niconistal/BabyBox/renders/v2-front.png

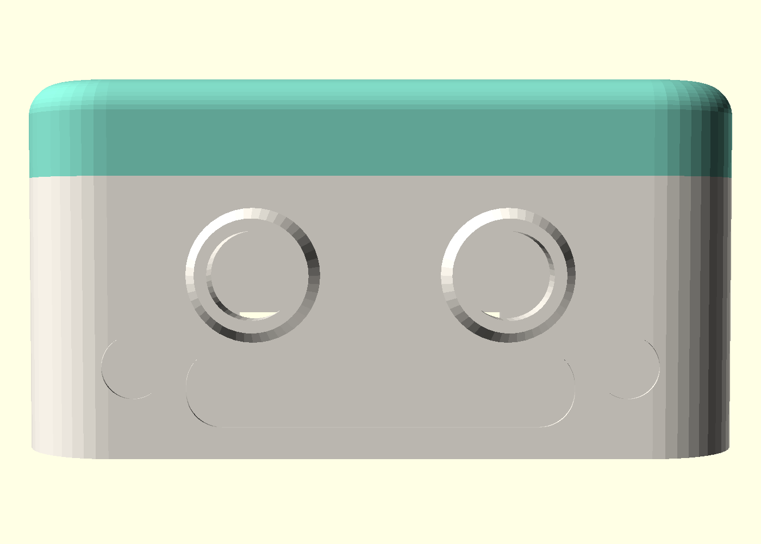
renders/v2-front.png
