niconistal/BabyBox/renders/v2-lid-under.png

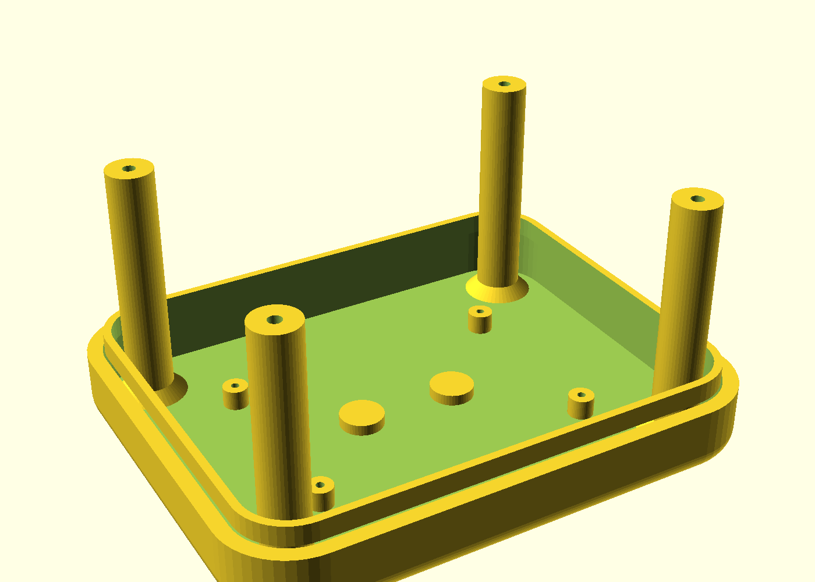
renders/v2-lid-under.png
