niconistal/BabyBox/renders/v3-hero.png

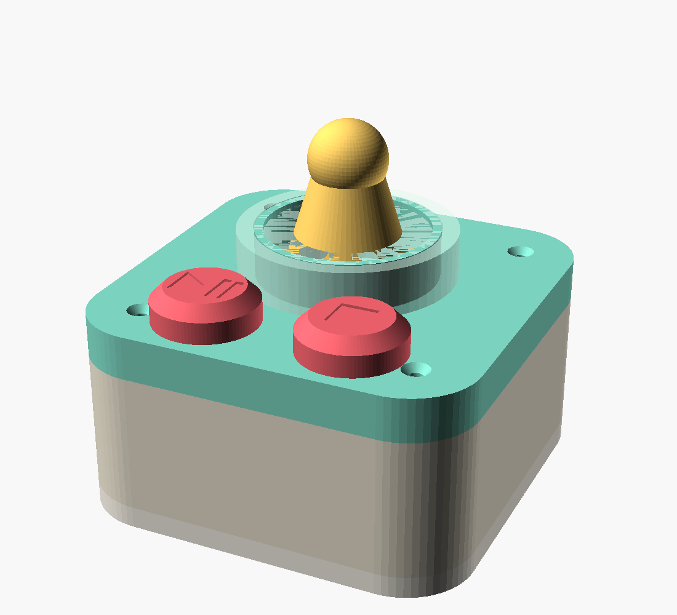
renders/v3-hero.png
