niconistal/BabyBox/website/images/v3-keycaps.png

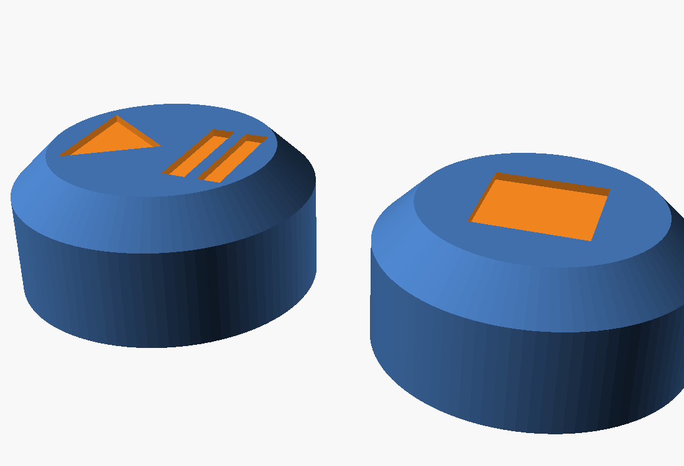
website/images/v3-keycaps.png
